devAM-22/Arduino-FM-radio/Kuvat/IMG20250411093300.jpg

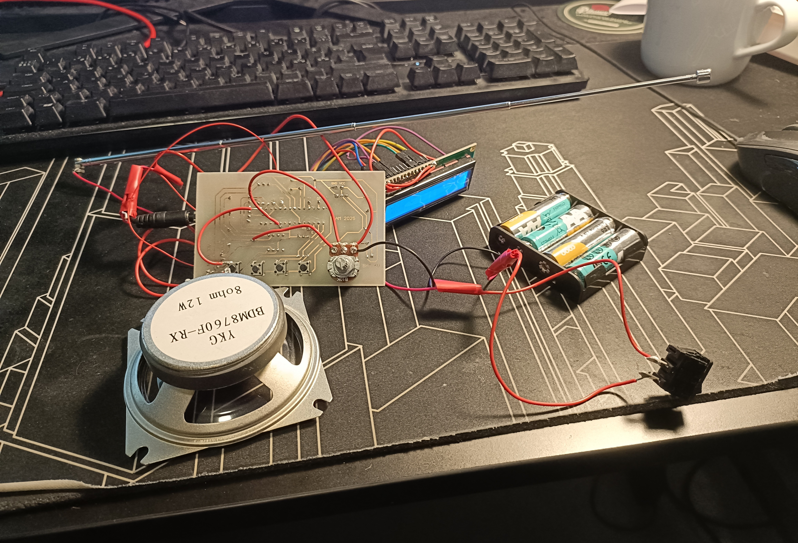
Kuvat/IMG20250411093300.jpg
